adamassi/IOT_CATCH_THE_FLAG/our_code/L298NX2.h

#ifndef L298NX2_h
#define L298NX2_h

#include "Arduino.h"
#include "L298N.h"

typedef void (*CallBackFunction)();

class L298NX2
{
public:
   L298NX2(
       uint8_t pinEnable_A,
       uint8_t pinIN1_A,
       uint8_t pinIN2_A,
       uint8_t pwmChannel_A,
       uint8_t pinEnable_B,
       uint8_t pinIN1_B,
       uint8_t pinIN2_B,
       uint8_t pwmChannel_B);

   L298NX2(uint8_t pinIN1_A,
           uint8_t pinIN2_A,
           uint8_t pinIN1_B,
           uint8_t pinIN2_B);

   // MOTOR A
   void setSpeedA(unsigned short pwmVal_A);
   unsigned short getSpeedA();
   void forwardA();
   void forwardForA(unsigned long delay_A, CallBackFunction callback_A);
   void forwardForA(unsigned long delay_A);
   void backwardA();
   void backwardForA(unsigned long delay_A, CallBackFunction callback_A);
   void backwardForA(unsigned long delay_A);
   void runA(L298N::Direction direction_A);
   void runForA(unsigned long delay_A, L298N::Direction direction_A);
   void runForA(unsigned long delay_A, L298N::Direction direction_A, CallBackFunction callback_A);
   void stopA();
   void resetA();
   boolean isMovingA();
   L298N::Direction getDirectionA();

   // MOTOR B
   void setSpeedB(unsigned short pwmVal_B);
   unsigned short getSpeedB();
   void forwardB();
   void forwardForB(unsigned long delay_B, CallBackFunction callback_B);
   void forwardForB(unsigned long delay_B);
   void backwardB();
   void backwardForB(unsigned long delay_B, CallBackFunction callback_B);
   void backwardForB(unsigned long delay_B);
   void runB(L298N::Direction direction_B);
   void runForB(unsigned long delay_B, L298N::Direction direction_B);
   void runForB(unsigned long delay_B, L298N::Direction direction_B, CallBackFunction callback_B);
   void stopB();
   void resetB();
   boolean isMovingB();
   L298N::Direction getDirectionB();

   // BOTH
   void setSpeed(unsigned short pwmVal);
   void forward();
   void forwardFor(unsigned long delay, CallBackFunction callback);
   void forwardFor(unsigned long delay);
   void backward();
   void backwardFor(unsigned long delay, CallBackFunction callback);
   void backwardFor(unsigned long delay);
   void run(L298N::Direction direction);
   void runFor(unsigned long delay, L298N::Direction direction);
   void runFor(unsigned long delay, L298N::Direction direction, CallBackFunction callback);
   void stop();
   void reset();

private:
   L298N _motorA;
   L298N _motorB;

   unsigned long _lastMs;
   boolean _canMove;

   static void fakeCallback();
};

#endif






























// #ifndef L298NX2_h
// #define L298NX2_h

// #include "Arduino.h"
// #include "L298N.h"

// typedef void (*CallBackFunction)();

// class L298NX2
// {
// public:
//    L298NX2(
//        uint8_t pinEnable_A,
//        uint8_t pinIN1_A,
//        uint8_t pinIN2_A,
//        uint8_t pinEnable_B,
//        uint8_t pinIN1_B,
//        uint8_t pinIN2_B);
//    L298NX2(uint8_t pinIN1_A,
//            uint8_t pinIN2_A,
//            uint8_t pinIN1_B,
//            uint8_t pinIN2_B);

//    //MOTOR A
//    void setSpeedA(unsigned short pwmVal_A);
//    unsigned short getSpeedA();
//    void forwardA();
//    void forwardForA(unsigned long delay_A, CallBackFunction callback_A);
//    void forwardForA(unsigned long delay_A);
//    void backwardA();
//    void backwardForA(unsigned long delay_A, CallBackFunction callback_A);
//    void backwardForA(unsigned long delay_A);
//    void runA(L298N::Direction direction_A);
//    void runForA(unsigned long delay_A, L298N::Direction direction_A);
//    void runForA(unsigned long delay_A, L298N::Direction direction_A, CallBackFunction callback_A);
//    void stopA();
//    void resetA();
//    boolean isMovingA();
//    L298N::Direction getDirectionA();

//    //MOTOR B
//    void setSpeedB(unsigned short pwmVal_B);
//    unsigned short getSpeedB();
//    void forwardB();
//    void forwardForB(unsigned long delay_B, CallBackFunction callback_B);
//    void forwardForB(unsigned long delay_B);
//    void backwardB();
//    void backwardForB(unsigned long delay_B, CallBackFunction callback_B);
//    void backwardForB(unsigned long delay_B);
//    void runB(L298N::Direction direction_B);
//    void runForB(unsigned long delay_B, L298N::Direction direction_B);
//    void runForB(unsigned long delay_B, L298N::Direction direction_B, CallBackFunction callback_B);
//    void stopB();
//    void resetB();
//    boolean isMovingB();
//    L298N::Direction getDirectionB();

//    //BOTH
//    void setSpeed(unsigned short pwmVal);
//    void forward();
//    void forwardFor(unsigned long delay, CallBackFunction callback);
//    void forwardFor(unsigned long delay);
//    void backward();
//    void backwardFor(unsigned long delay, CallBackFunction callback);
//    void backwardFor(unsigned long delay);
//    void run(L298N::Direction direction);
//    void runFor(unsigned long delay, L298N::Direction direction);
//    void runFor(unsigned long delay, L298N::Direction direction, CallBackFunction callback);
//    void stop();
//    void reset();

// private:
//    L298N _motorA;
//    L298N _motorB;

//    unsigned long _lastMs;
//    boolean _canMove;

//    static void fakeCallback();
// };

// #endif
