adamassi/IOT_CATCH_THE_FLAG/our_code/L298N.h

#ifndef L298N_h
#define L298N_h

#include "Arduino.h"

typedef void (*CallBackFunction)();

class L298N
{
public:
   typedef enum
   {
      FORWARD = 0,
      BACKWARD = 1,
      STOP = -1
   } Direction;

   // Updated constructor with PWM channel for ESP32
   L298N(uint8_t pinEnable, uint8_t pinIN1, uint8_t pinIN2, uint8_t pwmChannel);
   L298N(uint8_t pinIN1, uint8_t pinIN2); // for constant-speed use (jumper on EN)

   void setSpeed(unsigned short pwmVal);
   unsigned short getSpeed();
   void forward();
   void forwardFor(unsigned long delay, CallBackFunction callback);
   void forwardFor(unsigned long delay);
   void backward();
   void backwardFor(unsigned long delay, CallBackFunction callback);
   void backwardFor(unsigned long delay);
   void run(L298N::Direction direction);
   void runFor(unsigned long delay, L298N::Direction direction);
   void runFor(unsigned long delay, L298N::Direction direction, CallBackFunction callback);
   void stop();
   void reset();
   boolean isMoving();
   Direction getDirection();

private:
   byte _pinEnable;
   byte _pinIN1;
   byte _pinIN2;
   byte _pwmVal;
   byte _pwmChannel;
   unsigned long _lastMs;
   boolean _canMove;
   boolean _isMoving;
   L298N::Direction _direction;
   static void fakeCallback();
};

#endif

















// #ifndef L298N_h
// #define L298N_h

// #include "Arduino.h"

// typedef void (*CallBackFunction)();

// class L298N
// {
// public:
//    typedef enum
//    {
//       FORWARD = 0,
//       BACKWARD = 1,
//       STOP = -1
//    } Direction;

//    L298N(uint8_t pinEnable, uint8_t pinIN1, uint8_t pinIN2);
//    L298N(uint8_t pinIN1, uint8_t pinIN2);
//    void setSpeed(unsigned short pwmVal);
//    unsigned short getSpeed();
//    void forward();
//    void forwardFor(unsigned long delay, CallBackFunction callback);
//    void forwardFor(unsigned long delay);
//    void backward();
//    void backwardFor(unsigned long delay, CallBackFunction callback);
//    void backwardFor(unsigned long delay);
//    void run(L298N::Direction direction);
//    void runFor(unsigned long delay, L298N::Direction direction);
//    void runFor(unsigned long delay, L298N::Direction direction, CallBackFunction callback);
//    void stop();
//    void reset();
//    boolean isMoving();
//    Direction getDirection();

// private:
//    byte _pinEnable;
//    byte _pinIN1;
//    byte _pinIN2;
//    byte _pwmVal;
//    unsigned long _lastMs;
//    boolean _canMove;
//    boolean _isMoving;
//    L298N::Direction _direction;
//    static void fakeCallback();
// };

// #endif
